greatscottgadgets/ubertooth/host/kismet/plugin-ubertooth-phyneutral/README

Kismet-Ubertooth-Phyneutral

-1. PHY NEUTRAL

    Kismet is currently (Spring/Summer 2011) undergoing a rewrite of the
    internal system for tracking networks to make Kismet truly phy-neutral,
    agnostic of the type of data being sniffed and type of devices being
    tracked.

    This branch of the Ubertooth Kismet plugin uses the phy-neutral
    extensions in Kismet.  It REQUIRES the LATEST svn of Kismet as
    phy-neutral is a rapidly moving target and is being co-developed with
    the Ubertooth plugin and the phy-neutral 802.11 components.  IT WILL NOT
    work with NON-BLEEDING-EDGE Kismet.  Every time you update the Ubertooth
    plugin code, update Kismet and recompile it at the same time!

0.  NOT COMPLETE

1.  What is Kismet-Ubertooth
2.  Caveats
3.  Compiling
4.  Installing
5.  Using

0.  NOT COMPLETE

*** THIS CODE IS CURRENTLY NOT COMPLETE ***

What it does:

* Control one (and only one) Ubertooth Zero or Ubertooth One
* Monitor one Bluetooth channel
* Display the LAP of Bluetooth packets
* Determine and display the UAP of Bluetooth packets
* Log to pcap file

What it should be able to do in the future:

* Determine the clock of a target piconets
* Hop along with a target piconet through all channels
* Control more than one Ubertooth Zero or Ubertooth One
* Read pcap files
* Print debug info about packets

1.  What is Kismet-Ubertooth

	Kismet-Ubertooth is a Kismet plugin which provides Bluetooth support in
	Kismet.  It relies on the Bluetooth baseband library, libbtbb 
	(https://github.com/greatscottgadgets/libbtbb). Kismet-Ubertooth
	performs passive monitoring of Bluetooth networks using the Ubertooth
	platform (https://github.com/greatscottgadgets/ubertooth).

	It CAN NOT BE USED with 802.11 wi-fi cards, it is a completely different
	protocol.  If you do not have an Ubertooth but have a Bluetooth adapter,
	try the btscan plugin instead.  It performs active scanning of discoverable
	Bluetooth devices.  Better yet, build yourself an Ubertooth One.

	Kismet-Ubertooth defines the decoders, loggers, and UI controls for
	Bluetooth networks in a common fashion, and supports reading and writing
	Bluetooth baseband pcap files.

	The Bluetooth baseband protocol is the air interface of Bluetooth.  It
	operates in the 2.4 GHz ISM band.  There is a separate interface known as
	HCI (Host Controller Interface) that operates between a host computer and
	an attached Bluetooth adapter.  Kismet-Ubertooth uses special hardware to
	directly access the baseband layer.  It does not operate at the HCI layer.
	Try hcidump if you want to access HCI.

2.  Caveats

	This code is currently only partially developed and may not provide full
	functionality.

	This code has only been tested on Linux.  This code MAY work on other
	platforms, but currently it is only developed with Linux as a target.

3.  Compiling

	Compiling the Kismet-Ubertooth plugin requires the Kismet source be
	installed and configured.  The libbtbb library (0.5 or higher) and libusb
	(1.0 or higher) must also be installed.

	By default, Kismet-Ubertooth expects the Kismet source to be in
	/usr/src/kismet; this can be overridden by setting the KIS_SRC_DIR
	environment variable:

		cd plugin-ubertooth
		KIS_SRC_DIR=/home/foo/src/kismet make

4.  Installing

	Kismet plugins may be installed system-wide in the plugins directory (by
	default, /usr/local/lib/kismet/) or in the users home directory
	(~/.kismet/plugins).

	To install in the system-wide directory:

        cd plugin-ubertooth
        KIS_SRC_DIR=/home/foo/src/kismet make install

    Plugins can be installed in the current users home directory with:

        cd plugin-ubertooth
        make userinstall

5.  Using

	Once the plugin is loaded, Kismet will automatically understand and
	decode pcap files with the Bluetooth link data.

	To capture from an Ubertooth Zero or Ubertooth One, plug in the USB device,
	and define a capture source in Kismet using the interface 'ubertooth'.  The
	device will be automatically detected.

	If you have multiple Ubertooth devices connected, Kismet-Ubertooth uses the
	first one it finds.  Kismet-Ubertooth currently is not capable of using
	multiple Ubertooth devices simultaneously.

	To enable pcap logging, the logfile must be turned on by adding
	'pcapbtbb' to the logtypes= line of the kismet.conf.
