greatscottgadgets/ubertooth/hardware/endive/endive.sch

## KiCad design hardware/endive/endive.sch (2011-09-12)

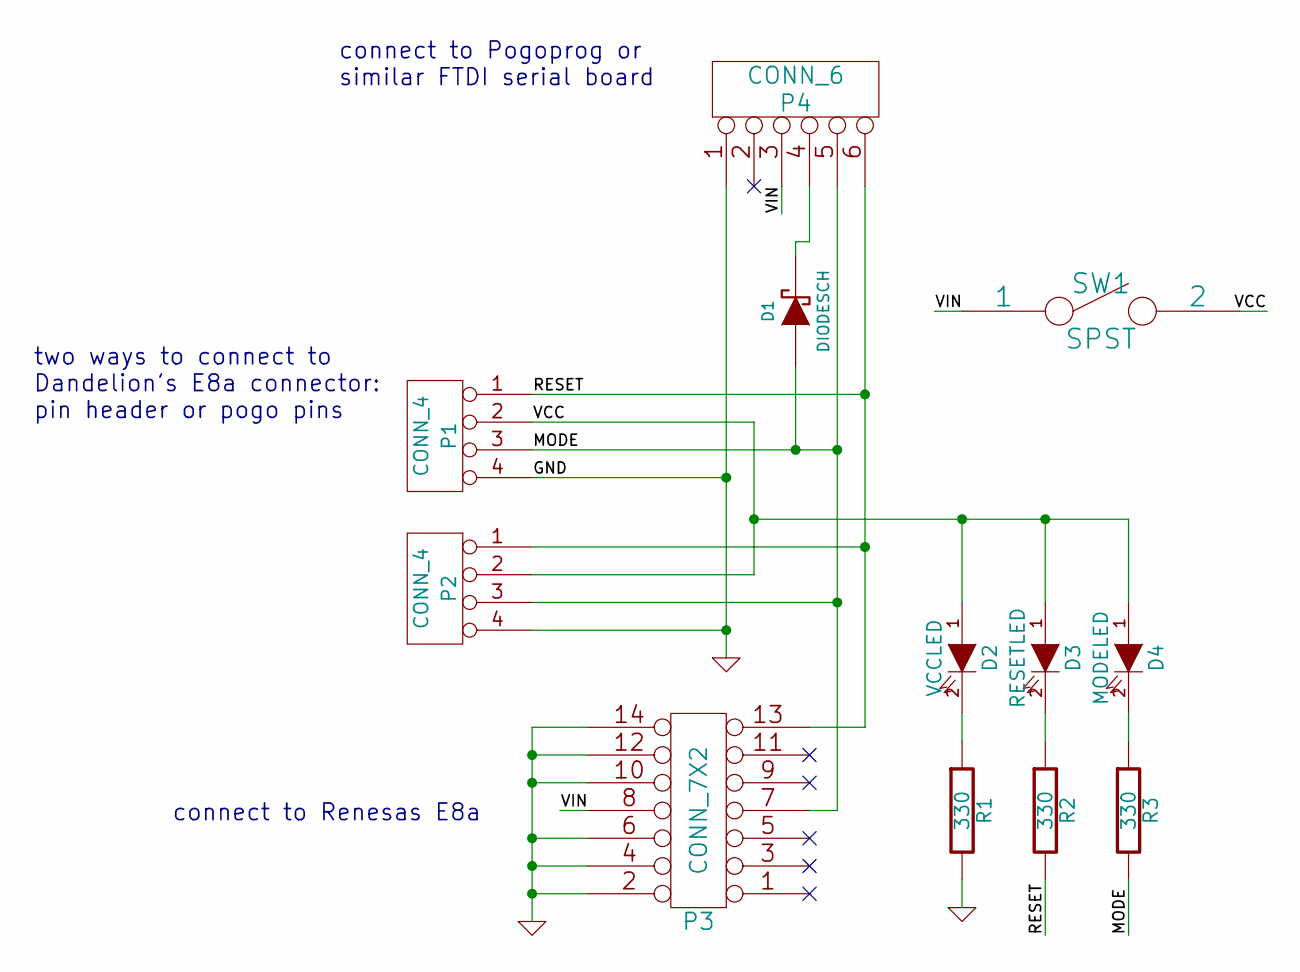
[picture p11: schematic endive.sch]

Parts:
D1: DIODESCH
D2: VCCLED
D3: RESETLED
D4: MODELED
P1, P2: CONN_4
P3: CONN_7X2
P4: CONN_6
R1, R2, R3: 330
SW1: SPST

Connections:
GND: P1.4, P2.4, P3.2, P3.4, P3.6, P3.10, P3.12, P3.14, P4.1, R1.2
MODE: D1.1 (A), P1.3, P2.3, P3.7, P4.5, R3.2
unnamed: D1.2 (K), P4.4
unnamed: D2.2 (K), R1.1
unnamed: D3.2 (K), R2.1
unnamed: D4.2 (K), R3.1
RESET: P1.1, P2.1, P3.13, P4.6, R2.2
VCC: D2.1 (A), D3.1 (A), D4.1 (A), P1.2, P2.2, SW1.2
VIN: P3.8, P4.3, SW1.1

Notes on the sheet:
connect to Renesas E8a
connect to Pogoprog or similar FTDI serial board
two ways to connect to Dandelion's E8a connector: pin header or pogo pins
