greatscottgadgets/ubertooth/hardware/pogoprog/pogoprog.sch

## KiCad design hardware/pogoprog/pogoprog.sch (2021-12-16)

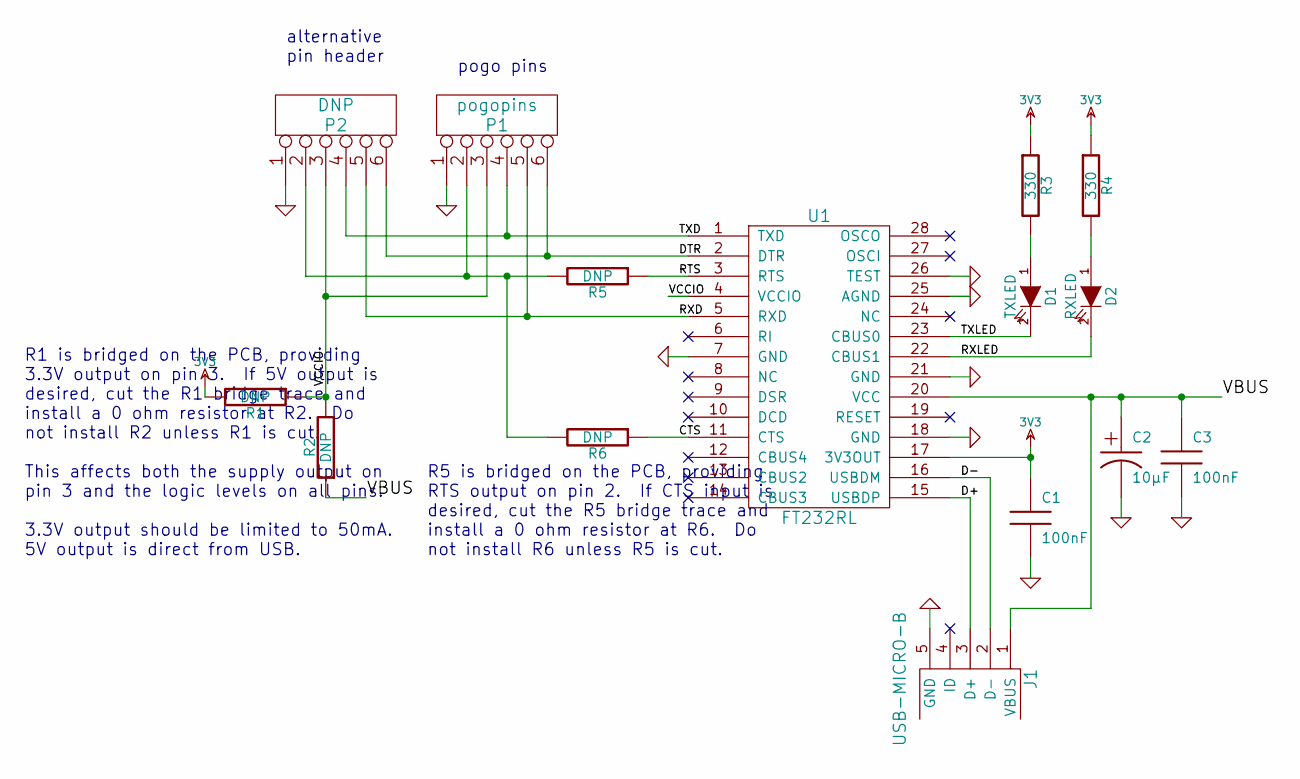
[picture p12: schematic pogoprog.sch]

Parts:
C1, C3: 100nF
C2: 10μF
D1: TXLED
D2: RXLED
J1: USB-MICRO-B
P1: pogopins
P2: DNP
R1, R2, R5, R6: DNP
R3, R4: 330
U1: FT232RL

Connections:
3V3: C1.1, R1.2, R3.1, R4.1, U1.17 (3V3OUT)
CTS: R6.1, U1.11 (CTS)
D+: J1.3 (D+), U1.15 (USBDP)
D-: J1.2 (D-), U1.16 (USBDM)
DTR: P1.6, P2.6, U1.2 (DTR)
GND: C1.2, C2.2, C3.2, J1.5 (GND), P1.1, P2.1, U1.7 (GND), U1.18 (GND), U1.21 (GND), U1.25 (AGND), U1.26 (TEST)
unnamed: D1.1 (A), R3.2
unnamed: D2.1 (A), R4.2
unnamed: P1.2, P2.2, R5.2, R6.2
RTS: R5.1, U1.3 (RTS)
RXD: P1.5, P2.5, U1.5 (RXD)
RXLED: D2.2 (K), U1.22 (CBUS1)
TXD: P1.4, P2.4, U1.1 (TXD)
TXLED: D1.2 (K), U1.23 (CBUS0)
VBUS: C2.1, C3.1, J1.1 (VBUS), R2.1, U1.20 (VCC)
VCCIO: P1.3, P2.3, R1.1, R2.2, U1.4 (VCCIO)

Notes on the sheet:
R5 is bridged on the PCB, providing RTS output on pin 2. If CTS input is desired, cut the R5 bridge trace and install a 0 ohm resistor at R6. Do not install R6 unless R5 is cut.
R1 is bridged on the PCB, providing 3.3V output on pin 3. If 5V output is desired, cut the R1 bridge trace and install a 0 ohm resistor at R2. Do not install R2 unless R1 is cut. This affects both the supply output on pin 3 and the logic levels on all pins. 3.3V output should be limited to 50mA. 5V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
alternative pin header
pogo pins
