greatscottgadgets/ubertooth/hardware/ubertooth-one/ubertooth-one.sch

## KiCad design hardware/ubertooth-one/ubertooth-one.sch (2021-12-16)

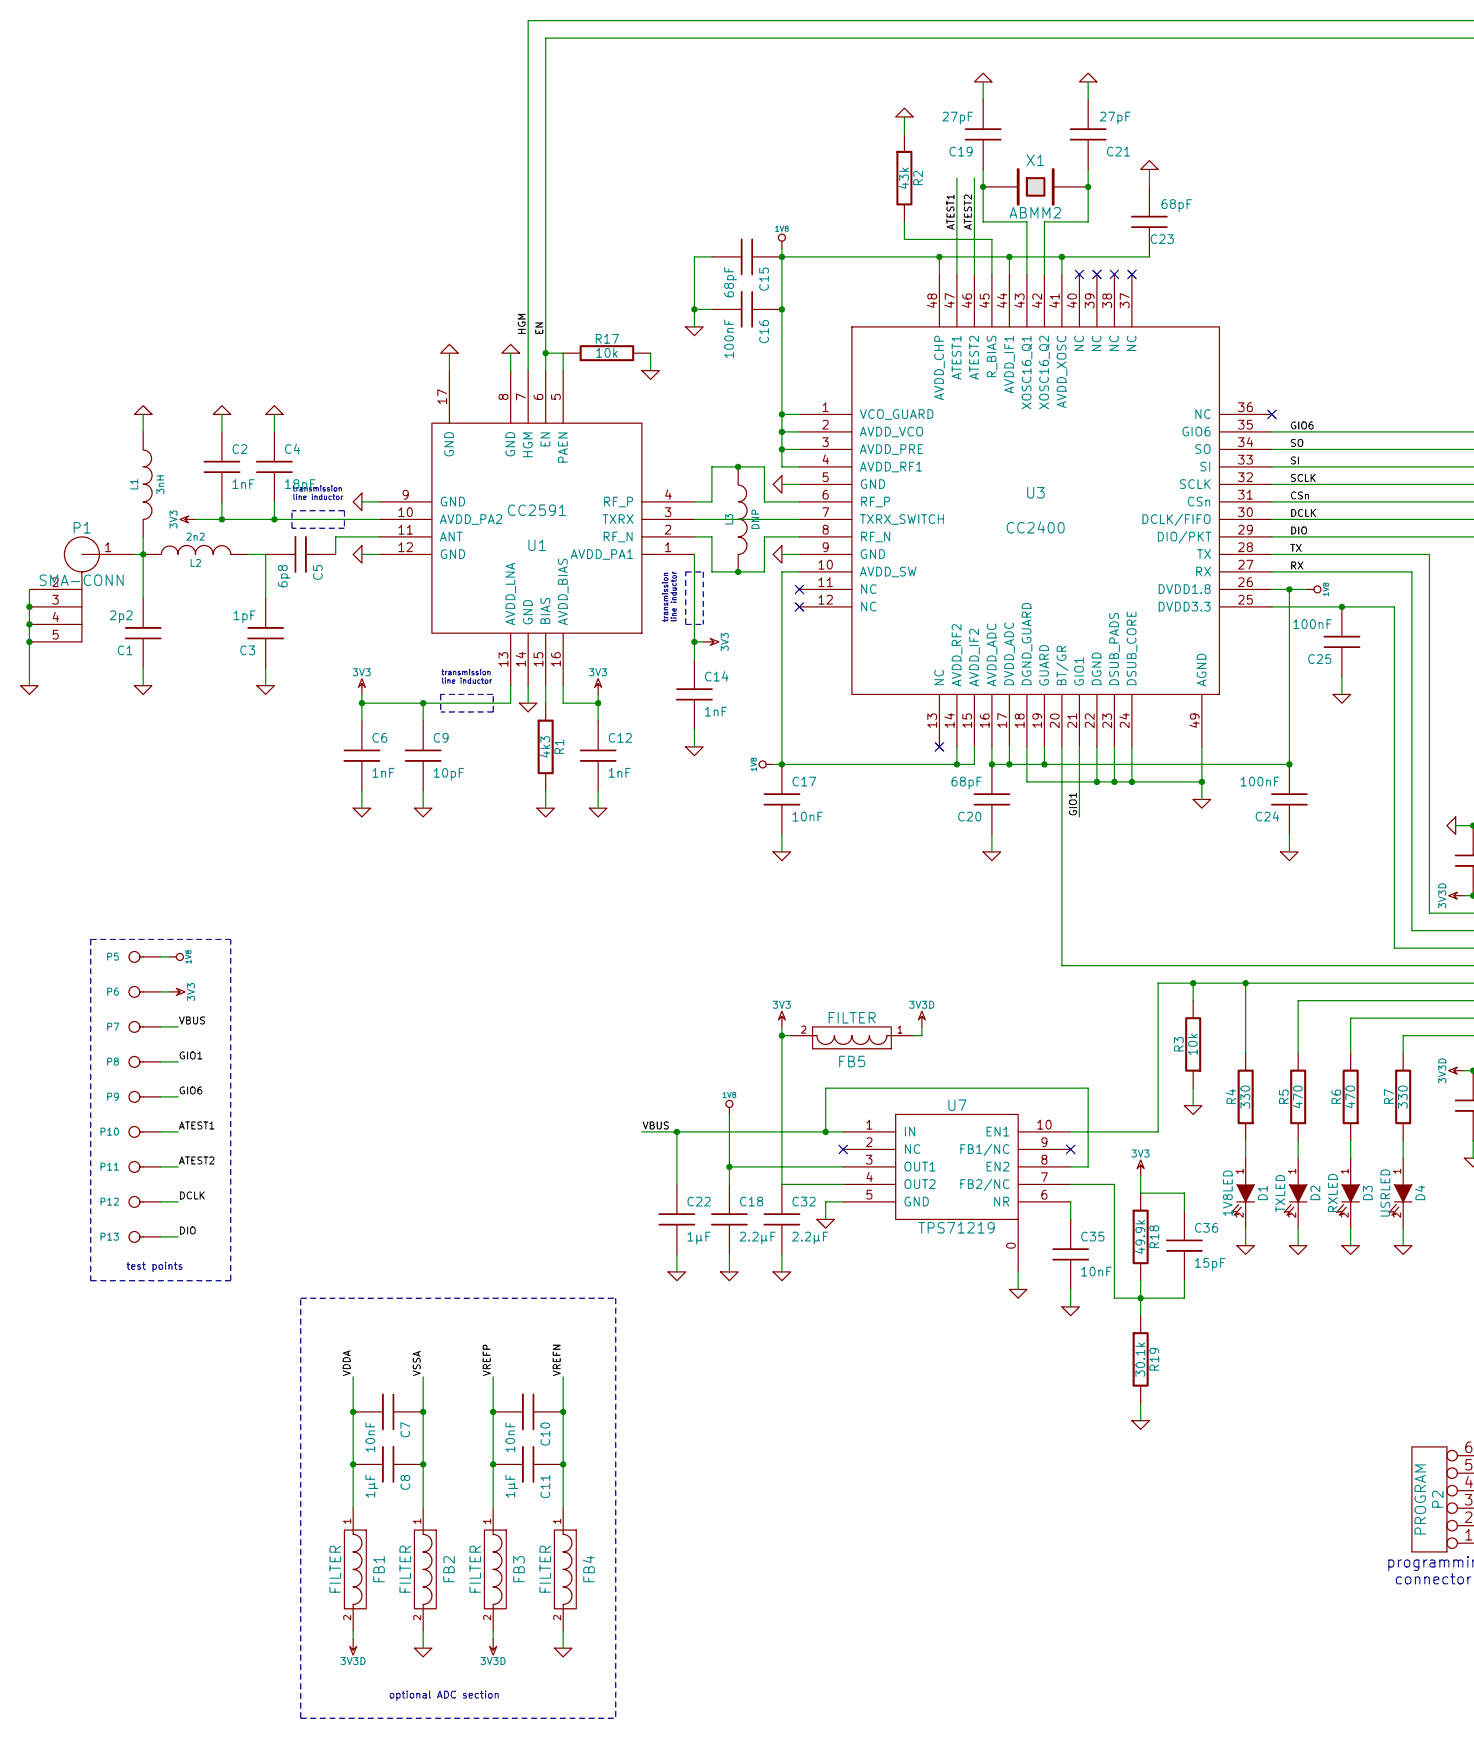
[picture p15: schematic ubertooth-one.sch, part in row 1, column 1]

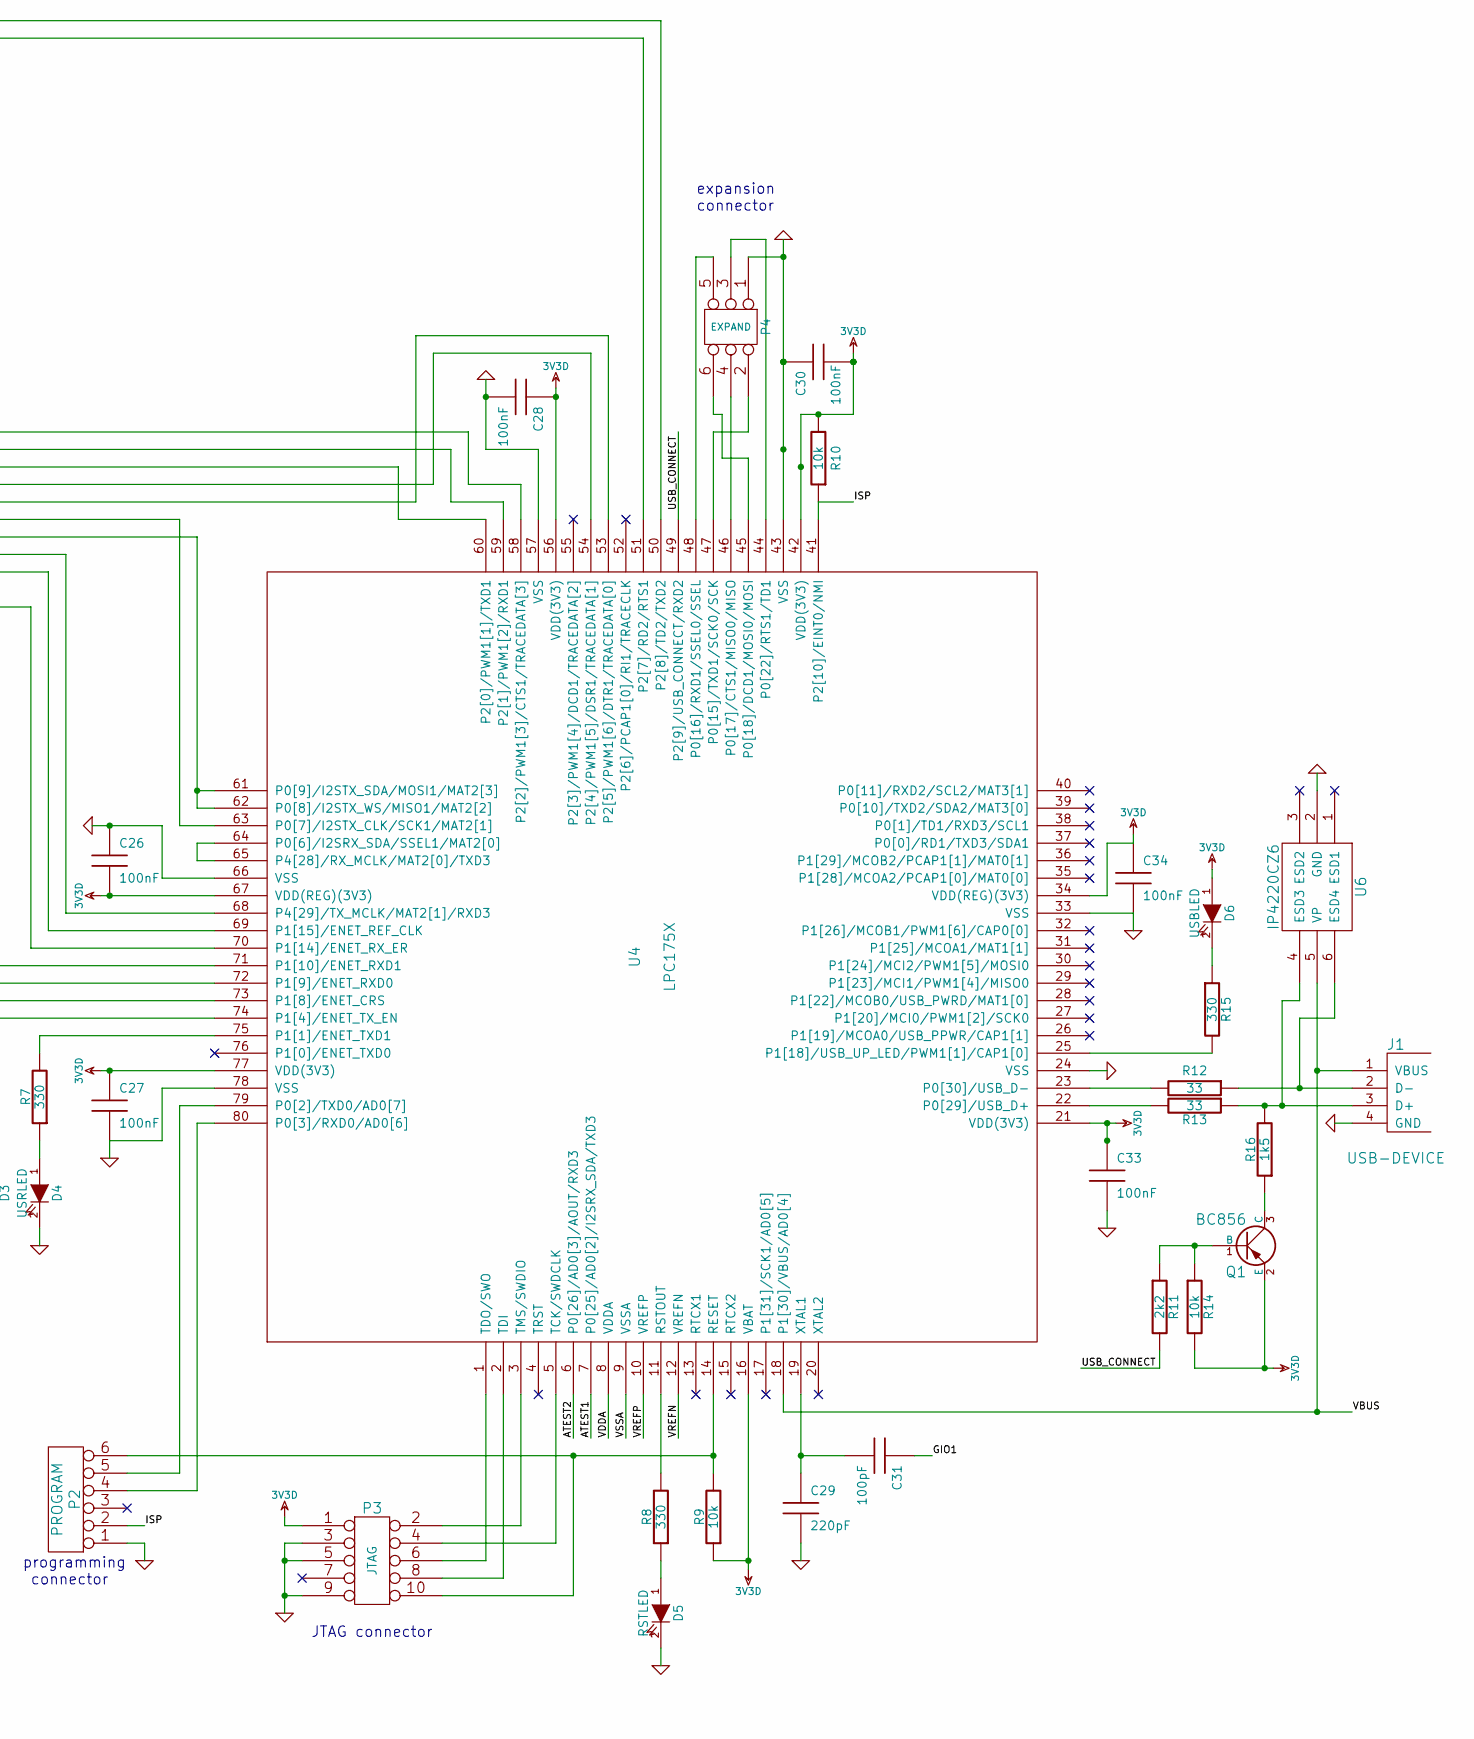
[picture p16: schematic ubertooth-one.sch, part in row 1, column 2]

Parts:
C1: 2p2; 0402
C2, C6, C12, C14: 1nF; 0402
C3: 1pF; 0402
C4: 18pF; 0402
C5: 6p8; 0402
C7, C10, C35: 10nF; 0603
C8, C11, C22: 1µF; 0603
C9: 10pF; 0402
C15, C20, C23: 68pF; 0402
C16, C24, C25: 100nF; 0402
C17: 10nF; 0402
C18, C32: 2.2µF; 0603
C19, C21: 27pF; 0603
C26, C27, C28, C30, C33, C34: 100nF; 0603
C29: 220pF; 0603
C31: 100pF; 0603
C36: 15pF; 0603
D1: 1V8LED; 0603D
D2: TXLED; 0603D
D3: RXLED; 0603D
D4: USRLED; 0603D
D5: RSTLED; 0603D
D6: USBLED; 0603D
FB1, FB2, FB3, FB4: FILTER; 0603bridged
FB5: FILTER; 0603
J1: USB-DEVICE; USB-A-USAM-04
L1: 3nH; 0402
L2: 2n2; 0402
L3: DNP; 0402gap
P1: SMA-CONN; SMA-EDGE
P2: PROGRAM; 100MIL-HEADER-1X6-EDGE
P3: JTAG; 50MIL-HEADER-2X5-TH
P4: EXPAND; PIN_ARRAY_3X2
P5: 1V8; testpad-50mil
P6: 3V3; testpad-50mil
P7: VBUS; testpad-50mil
P8: GIO1; testpad-50mil
P9: GIO6; testpad-50mil
P10: ATEST1; testpad-50mil
P11: ATEST2; testpad-50mil
P12: DCLK; testpad-50mil
P13: DIO; testpad-50mil
Q1: BC856; SOT416
R1: 4k3; 0402
R2: 43k; 0402
R3, R9, R10, R14, R17: 10k; 0603
R4, R7, R8, R15: 330; 0603
R5, R6: 470; 0603
R11: 2k2; 0603
R12, R13: 33; 0603
R16: 1k5; 0603
R18: 49.9k; 0603
R19: 30.1k; 0603
U1: CC2591; VQFN16
U3: CC2400; QFN48
U4: LPC175X; LQFP80
U6: IP4220CZ6; SOT457
U7: TPS71219; S-PVSON-N10
X1: ABMM2

Connections:
1V8: C15.1, C16.1, C17.1, C18.1, C20.2, C23.1, C24.2, P5.1, U3.1 (VCO_GUARD), U3.2 (AVDD_VCO), U3.3 (AVDD_PRE), U3.4 (AVDD_RF1), U3.10 (AVDD_SW), U3.14 (AVDD_RF2), U3.15 (AVDD_IF2), U3.16 (AVDD_ADC), U3.17 (DVDD_ADC), U3.19 (GUARD), U3.26 (DVDD1.8), U3.41 (AVDD_XOSC), U3.44 (AVDD_IF1), U3.48 (AVDD_CHP), U7.3 (OUT1)
3V3: C2.2, C4.2, C6.1, C9.1, C12.1, C14.1, C32.1, C36.1, FB5.2, P6.1, R18.1, U1.1 (AVDD_PA1), U1.10 (AVDD_PA2), U1.13 (AVDD_LNA), U1.16 (AVDD_BIAS), U7.4 (OUT2)
3V3D: C26.2, C27.1, C28.1, C30.2, C33.1, C34.1, D6.1 (A), FB1.2, FB3.2, FB5.1, P3.1, Q1.2 (E), R9.1, R10.2, R14.2, U4.16 (VBAT), U4.21 (VDD(3V3)), U4.34 (VDD(REG)(3V3)), U4.42 (VDD(3V3)), U4.56 (VDD(3V3)), U4.67 (VDD(REG)(3V3)), U4.77 (VDD(3V3))
ATEST1: P10.1, U3.47 (ATEST1), U4.7 (P0[25]/AD0[2]/I2SRX_SDA/TXD3)
ATEST2: P11.1, U3.46 (ATEST2), U4.6 (P0[26]/AD0[3]/AOUT/RXD3)
CSn: U3.31 (CSn), U4.53 (P2[5]/PWM1[6]/DTR1/TRACEDATA[0])
DCLK: P12.1, U3.30 (DCLK/FIFO), U4.63 (P0[7]/I2STX_CLK/SCK1/MAT2[1])
DIO: P13.1, U3.29 (DIO/PKT), U4.61 (P0[9]/I2STX_SDA/MOSI1/MAT2[3]), U4.62 (P0[8]/I2STX_WS/MISO1/MAT2[2])
EN: R17.1, U1.5 (PAEN), U1.6 (EN), U4.51 (P2[7]/RD2/RTS1)
GIO1: C31.1, P8.1, U3.21 (GIO1)
GIO6: P9.1, U3.35 (GIO6), U4.58 (P2[2]/PWM1[3]/CTS1/TRACEDATA[3])
GND: C1.1, C2.1, C3.1, C4.1, C6.2, C9.2, C12.2, C14.2, C15.2, C16.2, C17.2, C18.2, C19.2, C20.1, C21.2, C22.2, C23.2, C24.1, C25.1, C26.1, C27.2, C28.2, C29.2, C30.1, C32.2, C33.2, C34.2, C35.2, D1.2 (K), D2.2 (K), D3.2 (K), D4.2 (K), D5.2 (K), FB2.2, FB4.2, J1.4 (GND), L1.1, P1.2 (GND), P1.3 (GND), P1.4 (GND), P1.5 (GND), P2.1, P3.3, P3.5, P3.9, P4.1, R1.2, R2.1, R3.1, R17.2, R19.2, U1.8 (GND), U1.9 (GND), U1.12 (GND), U1.14 (GND), U1.17 (GND), U3.5 (GND), U3.9 (GND), U3.18 (DGND_GUARD), U3.22 (DGND), U3.23 (DSUB_PADS), U3.24 (DSUB_CORE), U3.49 (AGND), U4.24 (VSS), U4.33 (VSS), U4.43 (VSS), U4.57 (VSS), U4.66 (VSS), U4.78 (VSS), U6.2 (GND), U7.0, U7.5 (GND)
HGM: U1.7 (HGM), U4.50 (P2[8]/TD2/TXD2)
ISP: P2.2, R10.1, U4.41 (P2[10]/EINT0/NMI)
unnamed: C1.2, L1.2, L2.1, P1.1 (RF)
unnamed: C3.2, C5.2, L2.2
unnamed: C5.1, U1.11 (ANT)
unnamed: C19.1, U3.43 (XOSC16_Q1), X1.1
unnamed: C21.1, U3.42 (XOSC16_Q2), X1.2
unnamed: C25.2, U3.25 (DVDD3.3), U4.70 (P1[14]/ENET_RX_ER)
unnamed: C29.1, C31.2, U4.19 (XTAL1)
unnamed: C35.1, U7.6 (NR)
unnamed: C36.2, R18.2, R19.1, U7.7 (FB2/NC)
unnamed: D1.1 (A), R4.1
unnamed: D2.1 (A), R5.1
unnamed: D3.1 (A), R6.1
unnamed: D4.1 (A), R7.1
unnamed: D5.1 (A), R8.1
unnamed: D6.2 (K), R15.1
unnamed: J1.2 (D-), R12.1, U6.6 (ESD4)
unnamed: J1.3 (D+), R13.1, R16.2, U6.4 (ESD3)
unnamed: L3.1, U1.4 (RF_P), U3.6 (RF_P)
unnamed: L3.2, U1.2 (RF_N), U3.8 (RF_N)
unnamed: P2.4, U4.80 (P0[3]/RXD0/AD0[6])
unnamed: P2.5, U4.79 (P0[2]/TXD0/AD0[7])
unnamed: P2.6, P3.10, R9.2, U4.14 (RESET)
unnamed: P3.2, U4.3 (TMS/SWDIO)
unnamed: P3.4, U4.5 (TCK/SWDCLK)
unnamed: P3.6, U4.1 (TDO/SWO)
unnamed: P3.8, U4.2 (TDI)
unnamed: P4.2, U4.47 (P0[15]/TXD1/SCK0/SCK)
unnamed: P4.3, U4.44 (P0[22]/RTS1/TD1)
unnamed: P4.4, U4.46 (P0[17]/CTS1/MISO0/MISO)
unnamed: P4.5, U4.48 (P0[16]/RXD1/SSEL0/SSEL)
unnamed: P4.6, U4.45 (P0[18]/DCD1/MOSI0/MOSI)
unnamed: Q1.1 (B), R11.1, R14.1
unnamed: Q1.3 (C), R16.1
unnamed: R1.1, U1.15 (BIAS)
unnamed: R2.2, U3.45 (R_BIAS)
unnamed: R3.2, R4.2, U4.72 (P1[9]/ENET_RXD0), U7.10 (EN1)
unnamed: R5.2, U4.73 (P1[8]/ENET_CRS)
unnamed: R6.2, U4.74 (P1[4]/ENET_TX_EN)
unnamed: R7.2, U4.75 (P1[1]/ENET_TXD1)
unnamed: R8.2, U4.11 (RSTOUT)
unnamed: R12.2, U4.23 (P0[30]/USB_D-)
unnamed: R13.2, U4.22 (P0[29]/USB_D+)
unnamed: R15.2, U4.25 (P1[18]/USB_UP_LED/PWM1[1]/CAP1[0])
unnamed: U1.3 (TXRX), U3.7 (TXRX_SWITCH)
unnamed: U3.20 (BT/GR), U4.71 (P1[10]/ENET_RXD1)
unnamed: U4.64 (P0[6]/I2SRX_SDA/SSEL1/MAT2[0]), U4.65 (P4[28]/RX_MCLK/MAT2[0]/TXD3)
RX: U3.27 (RX), U4.69 (P1[15]/ENET_REF_CLK)
SCLK: U3.32 (SCLK), U4.54 (P2[4]/PWM1[5]/DSR1/TRACEDATA[1])
SI: U3.33 (SI), U4.60 (P2[0]/PWM1[1]/TXD1)
SO: U3.34 (SO), U4.59 (P2[1]/PWM1[2]/RXD1)
TX: U3.28 (TX), U4.68 (P4[29]/TX_MCLK/MAT2[1]/RXD3)
USB_CONNECT: R11.2, U4.49 (P2[9]/USB_CONNECT/RXD2)
VBUS: C22.1, J1.1 (VBUS), P7.1, U4.18 (P1[30]/VBUS/AD0[4]), U6.5 (VP), U7.1 (IN), U7.8 (EN2)
VDDA: C7.2, C8.2, FB1.1, U4.8 (VDDA)
VREFN: C10.1, C11.1, FB4.1, U4.12 (VREFN)
VREFP: C10.2, C11.2, FB3.1, U4.10 (VREFP)
VSSA: C7.1, C8.1, FB2.1, U4.9 (VSSA)

Notes on the sheet:
test points
expansion connector
JTAG connector
programming connector
optional ADC section
transmission line inductor
