greatscottgadgets/ubertooth/firmware/common/ubertooth.h

/*
 * Copyright 2010, 2011 Michael Ossmann
 *
 * This file is part of Project Ubertooth.
 *
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
 * You should have received a copy of the GNU General Public License
 * along with this program; see the file COPYING.  If not, write to
 * the Free Software Foundation, Inc., 51 Franklin Street,
 * Boston, MA 02110-1301, USA.
 */

#ifndef __UBERTOOTH_H
#define __UBERTOOTH_H

#include "lpc17.h"
#include "types.h"
#include "cc2400.h"
#include "ubertooth_interface.h"

typedef void (*IAP_ENTRY)(u32[], u32[]);
extern const IAP_ENTRY iap_entry;

/* operating modes */
enum operating_modes {
	MODE_IDLE          = 0,
	MODE_RX_SYMBOLS    = 1,
	MODE_TX_SYMBOLS    = 2,
	MODE_TX_TEST       = 3,
	MODE_SPECAN        = 4,
	MODE_RANGE_TEST    = 5,
	MODE_REPEATER      = 6,
	MODE_LED_SPECAN    = 7,
	MODE_BT_FOLLOW     = 8,
	MODE_BT_FOLLOW_LE  = 9,
	MODE_BT_PROMISC_LE = 10,
	MODE_RESET         = 11,
	MODE_BT_SLAVE_LE   = 12,
	MODE_EGO           = 13,
	MODE_AFH           = 14,
	MODE_RX_GENERIC    = 15,
	MODE_TX_GENERIC    = 16,
	MODE_XMAS          = 17,
};

/* hardware identification number */
#define BOARD_ID_UBERTOOTH_ZERO 0
#define BOARD_ID_UBERTOOTH_ONE  1
#define BOARD_ID_TC13BADGE      2

#ifdef UBERTOOTH_ZERO
#define BOARD_ID BOARD_ID_UBERTOOTH_ZERO
#endif
#ifdef UBERTOOTH_ONE
#define BOARD_ID BOARD_ID_UBERTOOTH_ONE
#endif
#ifdef TC13BADGE
#define BOARD_ID BOARD_ID_TC13BADGE
#endif

/* GPIO pins */
#ifdef UBERTOOTH_ZERO
#define PIN_USRLED (1 << 11) /* P0.11 */
#define PIN_RXLED  (1 << 28) /* P4.28 */
#define PIN_TXLED  (1 << 29) /* P4.29 */
#define PIN_CC1V8  (1 << 29) /* P1.29 */
#define PIN_CC3V3  (1 << 0 ) /* P1.0  */
#define PIN_VBUS   (1 << 30) /* P1.30 */
#define PIN_RX     (1 << 1 ) /* P1.1  */
#define PIN_TX     (1 << 4 ) /* P1.4  */
#define PIN_CSN    (1 << 8 ) /* P1.8  */
#define PIN_SCLK   (1 << 9 ) /* P1.9  */
#define PIN_MOSI   (1 << 10) /* P1.10 */
#define PIN_MISO   (1 << 14) /* P1.14 */
#define PIN_GIO6   (1 << 15) /* P1.15 */
#define PIN_BTGR   (1 << 31) /* P1.31 */
#define PIN_SSEL0  (1 << 9 ) /* P2.9  */
#endif
#ifdef UBERTOOTH_ONE
#define PIN_USRLED (1 << 1 ) /* P1.1  */
#define PIN_RXLED  (1 << 4 ) /* P1.4  */
#define PIN_TXLED  (1 << 8 ) /* P1.8  */
#define PIN_CC1V8  (1 << 9 ) /* P1.9  */
#define PIN_CC3V3  (1 << 14) /* P1.14 */
#define PIN_VBUS   (1 << 30) /* P1.30 */
#define PIN_RX     (1 << 15) /* P1.15 */
#define PIN_TX     (1 << 29) /* P4.29 */
#define PIN_CSN    (1 << 5 ) /* P2.5  */
#define PIN_SCLK   (1 << 4 ) /* P2.4  */
#define PIN_MOSI   (1 << 0 ) /* P2.0  */
#define PIN_MISO   (1 << 1 ) /* P2.1  */
#define PIN_GIO6   (1 << 2 ) /* P2.2  */
#define PIN_BTGR   (1 << 10) /* P1.10 */
#define PIN_SSEL1  (1 << 28) /* P4.28 */
#define PIN_PAEN   (1 << 7 ) /* P2.7 */
#define PIN_HGM    (1 << 8 ) /* P2.8 */
#endif
#ifdef TC13BADGE
#define PIN_CC1V8    (1 << 0 ) /* P1.0  */
#define PIN_CC3V3    (1 << 14) /* P1.14 */
#define PIN_VBUS     (1 << 30) /* P1.30 */
#define PIN_DIGITAL2 (1 << 0 ) /* P2.0  */
#define PIN_DIGITAL3 (1 << 1 ) /* P2.1  */
#define PIN_DIGITAL4 (1 << 2 ) /* P2.2  */
#define PIN_DIGITAL5 (1 << 3 ) /* P2.3  */
#define PIN_DIGITAL6 (1 << 4 ) /* P2.4  */
#define PIN_DIGITAL7 (1 << 5 ) /* P2.5  */
#define PIN_DIGITAL8 (1 << 6 ) /* P2.6  */
#define PIN_DIGITAL9 (1 << 7 ) /* P2.7  */
#define PIN_SW1      (1 << 8 ) /* P2.8  */
#define PIN_CSN      (1 << 1 ) /* P1.1  */
#define PIN_SCLK     (1 << 4 ) /* P1.4  */
#define PIN_MOSI     (1 << 8 ) /* P1.8  */
#define PIN_MISO     (1 << 9 ) /* P1.9  */
#define PIN_GIO6     (1 << 10) /* P1.10 */
#define PIN_SSEL1    (1 << 28) /* P4.28 */
#define PIN_R8C_CTL  (1 << 22) /* P1.22 connects to R8C's P4_5 */
#define PIN_R8C_ACK  (1 << 19) /* P1.19 connects to R8C's P0_0 */
/* RX, TX, and BT/GR are fixed to ground on TC13BADGE */
#endif

/* indicator LED control */
#ifdef UBERTOOTH_ZERO
#define USRLED     (FIO0PIN & PIN_USRLED)
#define USRLED_SET (FIO0SET = PIN_USRLED)
#define USRLED_CLR (FIO0CLR = PIN_USRLED)
#define RXLED      (FIO4PIN & PIN_RXLED)
#define RXLED_SET  (FIO4SET = PIN_RXLED)
#define RXLED_CLR  (FIO4CLR = PIN_RXLED)
#define TXLED      (FIO4PIN & PIN_TXLED)
#define TXLED_SET  (FIO4SET = PIN_TXLED)
#define TXLED_CLR  (FIO4CLR = PIN_TXLED)
#endif
#ifdef UBERTOOTH_ONE
#define USRLED     (FIO1PIN & PIN_USRLED)
#define USRLED_SET (FIO1SET = PIN_USRLED)
#define USRLED_CLR (FIO1CLR = PIN_USRLED)
#define RXLED      (FIO1PIN & PIN_RXLED)
#define RXLED_SET  (FIO1SET = PIN_RXLED)
#define RXLED_CLR  (FIO1CLR = PIN_RXLED)
#define TXLED      (FIO1PIN & PIN_TXLED)
#define TXLED_SET  (FIO1SET = PIN_TXLED)
#define TXLED_CLR  (FIO1CLR = PIN_TXLED)
#endif
#ifdef TC13BADGE
//FIXME The LEDs need to be controlled by talking to the R8C.
#define USRLED     0
#define USRLED_SET
#define USRLED_CLR
#define RXLED      0
#define RXLED_SET
#define RXLED_CLR
#define TXLED      0
#define TXLED_SET
#define TXLED_CLR
#endif

/* SW1 button press */
#ifdef TC13BADGE
#define SW1 (FIO2PIN & PIN_SW1)
#endif

/* R8C control */
#ifdef TC13BADGE
#define R8C_CTL_SET (FIO1SET = PIN_R8C_CTL)
#define R8C_CTL_CLR (FIO1CLR = PIN_R8C_CTL)
#define R8C_ACK     (FIO1PIN & PIN_R8C_ACK)
#endif

/* SSEL (SPI slave select) control for CC2400 DIO (un-buffered) serial */
#ifdef UBERTOOTH_ZERO
#define DIO_SSEL_SET  (FIO2SET = PIN_SSEL0)
#define DIO_SSEL_CLR  (FIO2CLR = PIN_SSEL0)
#endif
#if defined UBERTOOTH_ONE || defined TC13BADGE
#define DIO_SSEL_SET  (FIO4SET = PIN_SSEL1)
#define DIO_SSEL_CLR  (FIO4CLR = PIN_SSEL1)
#endif

/* 1V8 regulator control */
#define CC1V8      (FIO1PIN & PIN_CC1V8)
#define CC1V8_SET  (FIO1SET = PIN_CC1V8)
#define CC1V8_CLR  (FIO1CLR = PIN_CC1V8)

/* CC2400 control */
#ifdef UBERTOOTH_ZERO
#define CC3V3_SET  (FIO1SET = PIN_CC3V3)
#define CC3V3_CLR  (FIO1CLR = PIN_CC3V3)
#define RX_SET     (FIO1SET = PIN_RX)
#define RX_CLR     (FIO1CLR = PIN_RX)
#define TX_SET     (FIO1SET = PIN_TX)
#define TX_CLR     (FIO1CLR = PIN_TX)
#define CSN_SET    (FIO1SET = PIN_CSN)
#define CSN_CLR    (FIO1CLR = PIN_CSN)
#define SCLK_SET   (FIO1SET = PIN_SCLK)
#define SCLK_CLR   (FIO1CLR = PIN_SCLK)
#define MOSI_SET   (FIO1SET = PIN_MOSI)
#define MOSI_CLR   (FIO1CLR = PIN_MOSI)
#define GIO6       (FIO2PIN & PIN_GIO6)
#define GIO6_SET   (FIO1SET = PIN_GIO6)
#define GIO6_CLR   (FIO1CLR = PIN_GIO6)
#define BTGR_SET   (FIO1SET = PIN_BTGR)
#define BTGR_CLR   (FIO1CLR = PIN_BTGR)
#define MISO       (FIO1PIN & PIN_MISO)
#endif
#ifdef UBERTOOTH_ONE
#define CC3V3_SET  (FIO1SET = PIN_CC3V3)
#define CC3V3_CLR  (FIO1CLR = PIN_CC3V3)
#define RX_SET     (FIO1SET = PIN_RX)
#define RX_CLR     (FIO1CLR = PIN_RX)
#define TX_SET     (FIO4SET = PIN_TX)
#define TX_CLR     (FIO4CLR = PIN_TX)
#define CSN_SET    (FIO2SET = PIN_CSN)
#define CSN_CLR    (FIO2CLR = PIN_CSN)
#define SCLK_SET   (FIO2SET = PIN_SCLK)
#define SCLK_CLR   (FIO2CLR = PIN_SCLK)
#define MOSI_SET   (FIO2SET = PIN_MOSI)
#define MOSI_CLR   (FIO2CLR = PIN_MOSI)
#define GIO6       (FIO2PIN & PIN_GIO6)
#define GIO6_SET   (FIO2SET = PIN_GIO6)
#define GIO6_CLR   (FIO2CLR = PIN_GIO6)
#define BTGR_SET   (FIO1SET = PIN_BTGR)
#define BTGR_CLR   (FIO1CLR = PIN_BTGR)
#define MISO       (FIO2PIN & PIN_MISO)
#endif
#ifdef TC13BADGE
#define CC3V3_SET  (FIO1SET = PIN_CC3V3)
#define CC3V3_CLR  (FIO1CLR = PIN_CC3V3)
#define CSN_SET    (FIO1SET = PIN_CSN)
#define CSN_CLR    (FIO1CLR = PIN_CSN)
#define SCLK_SET   (FIO1SET = PIN_SCLK)
#define SCLK_CLR   (FIO1CLR = PIN_SCLK)
#define MOSI_SET   (FIO1SET = PIN_MOSI)
#define MOSI_CLR   (FIO1CLR = PIN_MOSI)
#define GIO6       (FIO2PIN & PIN_GIO6)
#define GIO6_SET   (FIO1SET = PIN_GIO6)
#define GIO6_CLR   (FIO1CLR = PIN_GIO6)
#define MISO       (FIO1PIN & PIN_MISO)
#endif

/*
 * DIO_SSP is the SSP assigned to the CC2400's secondary ("un-buffered") serial
 * interface
 */
#ifdef UBERTOOTH_ZERO
#define DIO_SSP_CR0   SSP0CR0
#define DIO_SSP_CR1   SSP0CR1
#define DIO_SSP_DR    SSP0DR
#define DIO_SSP_DMACR SSP0DMACR
#define DIO_SSP_SRC   (1 << 1) /* for DMACCxConfig register */
#endif
#if defined UBERTOOTH_ONE || defined TC13BADGE
#define DIO_SSP_CR0   SSP1CR0
#define DIO_SSP_CR1   SSP1CR1
#define DIO_SSP_DR    SSP1DR
#define DIO_SSP_DMACR SSP1DMACR
#define DIO_SSP_SRC   (3 << 1) /* for DMACCxConfig register */
#endif

/* CC2591 control */
#ifdef UBERTOOTH_ONE
#define PAEN     (FIO2PIN & PIN_PAEN)
#define PAEN_SET (FIO2SET = PIN_PAEN)
#define PAEN_CLR (FIO2CLR = PIN_PAEN)
#define HGM      (FIO2PIN & PIN_HGM)
#define HGM_SET  (FIO2SET = PIN_HGM)
#define HGM_CLR  (FIO2CLR = PIN_HGM)
#endif

/* USB VBUS monitoring */
#define VBUS (FIO1PIN & PIN_VBUS)

/*
 * clock configuration
 *
 * main oscillator:  16 MHz (from CC2400)
 * CPU clock (PLL0): 100 MHz
 * USB clock (PLL1): 48 MHz
 *
 * The ToorCon 13 badge is configured with a 30 MHz CPU clock instead of 100
 * MHz to reduce heat at the voltage regulator.  This is a sufficient clock
 * speed for passive Bluetooth monitoring.
 */
#ifdef TC13BADGE
#define MSEL0 14
#define NSEL0 0
#define CCLKSEL 15
#else
#define MSEL0 24
#define NSEL0 1
#define CCLKSEL 3
#endif
#define MSEL1 34
#define PSEL1 0

/* flash accelerator configuration */
#define FLASHTIM 0x4 /* up to 100 MHz CPU clock */

/*
 * bootloader_ctrl is a fixed memory location used for passing
 * information from the application to the bootloader across a reset
 */
extern uint32_t bootloader_ctrl;
#define DFU_MODE 0x4305BB21

void wait(u8 seconds);
void wait_ms(u32 ms);
void wait_us(u32 us);
u32 rbit(u32 value);
void gpio_init(void);
void all_pins_off(void);
void ubertooth_init(void);
void dio_ssp_init(void);
void atest_init(void);
void cc2400_init(void);
u32 cc2400_spi(u8 len, u32 data);
u16 cc2400_get(u8 reg);
void cc2400_set(u8 reg, u16 val);
u8 cc2400_get8(u8 reg);
void cc2400_set8(u8 reg, u8 val);
void cc2400_fifo_write(u8 len, u8 *data);
void cc2400_fifo_read(u8 len, u8 *buf);
u8 cc2400_status(void);
u8 cc2400_strobe(u8 reg);
void cc2400_reset(void);
void clock_start(void);
void reset(void);
void r8c_takeover(void);
void cc2400_tune_rx(uint16_t channel);
void cc2400_tune_tx(uint16_t channel);
void cc2400_hop_rx(uint16_t channel);
void cc2400_hop_tx(uint16_t channel);
void get_part_num(uint8_t *buffer, int *len);
void get_device_serial(uint8_t *buffer, int *len);
void set_isp(void);

#endif /* __UBERTOOTH_H */
