greatscottgadgets/ubertooth/firmware/bluetooth_rxtx/ubertooth_usb.c

/*
 * Copyright 2010 Michael Ossmann
 * Copyright 2013 Dominic Spill
 *
 * This file is part of Project Ubertooth.
 *
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
 * You should have received a copy of the GNU General Public License
 * along with this program; see the file COPYING.  If not, write to
 * the Free Software Foundation, Inc., 51 Franklin Street,
 * Boston, MA 02110-1301, USA.
 */

/*
	LPCUSB, an USB device driver for LPC microcontrollers
	Copyright (C) 2006 Bertrik Sikken (bertrik@sikken.nl)

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
	1. Redistributions of source code must retain the above copyright
	   notice, this list of conditions and the following disclaimer.
	2. Redistributions in binary form must reproduce the above copyright
	   notice, this list of conditions and the following disclaimer in the
	   documentation and/or other materials provided with the distribution.
	3. The name of the author may not be used to endorse or promote products
	   derived from this software without specific prior written permission.

	THIS SOFTWARE IS PROVIDED BY THE AUTHOR ``AS IS'' AND ANY EXPRESS OR
	IMPLIED WARRANTIES, INCLUDING, BUT NOT LIMITED TO, THE IMPLIED WARRANTIES
	OF MERCHANTABILITY AND FITNESS FOR A PARTICULAR PURPOSE ARE DISCLAIMED.
	IN NO EVENT SHALL THE AUTHOR BE LIABLE FOR ANY DIRECT, INDIRECT,
	INCIDENTAL, SPECIAL, EXEMPLARY, OR CONSEQUENTIAL DAMAGES (INCLUDING, BUT
	NOT LIMITED TO, PROCUREMENT OF SUBSTITUTE GOODS OR SERVICES; LOSS OF USE,
	DATA, OR PROFITS; OR BUSINESS INTERRUPTION) HOWEVER CAUSED AND ON ANY
	THEORY OF LIABILITY, WHETHER IN CONTRACT, STRICT LIABILITY, OR TORT
	(INCLUDING NEGLIGENCE OR OTHERWISE) ARISING IN ANY WAY OUT OF THE USE OF
	THIS SOFTWARE, EVEN IF ADVISED OF THE POSSIBILITY OF SUCH DAMAGE.
*/

#include "usbapi.h"
#include "usbhw_lpc.h"
#include "ubertooth.h"
#include "ubertooth_usb.h"
#include <string.h>

#ifdef UBERTOOTH_ZERO
#define ID_VENDOR 0x1D50
#define ID_PRODUCT 0x6000
#elif defined UBERTOOTH_ONE
#define ID_VENDOR 0x1D50
#define ID_PRODUCT 0x6002
#elif defined TC13BADGE
#define ID_VENDOR 0xFFFF
#define ID_PRODUCT 0x0004
#else
#define ID_VENDOR 0xFFFF
#define ID_PRODUCT 0x0004
#endif

#define BULK_IN_EP		0x82
#define BULK_OUT_EP		0x05

#define MAX_PACKET_SIZE	64

#define LE_WORD(x)		((x)&0xFF),((x)>>8)

/*
 * This is supposed to be a lock-free ring buffer, but I haven't verified
 * atomicity of the operations on head and tail.
 */

static u8 abDescriptors[] = {

/* Device descriptor */
	0x12,
	DESC_DEVICE,
	LE_WORD(0x0200),		// bcdUSB
	0xFF,              		// bDeviceClass
	0x00,              		// bDeviceSubClass
	0x00,              		// bDeviceProtocol
	MAX_PACKET_SIZE0,  		// bMaxPacketSize
	LE_WORD(ID_VENDOR),		// idVendor
	LE_WORD(ID_PRODUCT),		// idProduct
	LE_WORD(0x0107),		// bcdDevice
	0x01,              		// iManufacturer
	0x02,              		// iProduct
	0x03,              		// iSerialNumber
	0x01,              		// bNumConfigurations

// configuration
	0x09,
	DESC_CONFIGURATION,
	LE_WORD(0x20),  		// wTotalLength
	0x01,  					// bNumInterfaces
	0x01,  					// bConfigurationValue
	0x00,  					// iConfiguration
	0x80,  					// bmAttributes
	0x6e,  					// bMaxPower (220mA)

// interface
	0x09,
	DESC_INTERFACE,
	0x00,  		 			// bInterfaceNumber
	0x00,   				// bAlternateSetting
	0x02,   				// bNumEndPoints
	0xFF,   				// bInterfaceClass
	0x00,   				// bInterfaceSubClass
	0x00,   				// bInterfaceProtocol
	0x00,   				// iInterface

// bulk in
	0x07,
	DESC_ENDPOINT,
	BULK_IN_EP,				// bEndpointAddress
	0x02,   				// bmAttributes = BULK
	LE_WORD(MAX_PACKET_SIZE),// wMaxPacketSize
	0,						// bInterval

// bulk out
	0x07,
	DESC_ENDPOINT,
	BULK_OUT_EP,			// bEndpointAddress
	0x02,   				// bmAttributes = BULK
	LE_WORD(MAX_PACKET_SIZE),// wMaxPacketSize
	0,						// bInterval

// string descriptors
	0x04,
	DESC_STRING,
	LE_WORD(0x0409),

	// manufacturer string
	40,
	DESC_STRING,
	'G', 0x00,
	'r', 0x00,
	'e', 0x00,
	'a', 0x00,
	't', 0x00,
	' ', 0x00,
	'S', 0x00,
	'c', 0x00,
	'o', 0x00,
	't', 0x00,
	't', 0x00,
	' ', 0x00,
	'G', 0x00,
	'a', 0x00,
	'd', 0x00,
	'g', 0x00,
	'e', 0x00,
	't', 0x00,
	's', 0x00,

	// product string
	28,
	DESC_STRING,
	'U', 0x00,
	'b', 0x00,
	'e', 0x00,
	'r', 0x00,
	't', 0x00,
	'o', 0x00,
	'o', 0x00,
	't', 0x00,
	'h', 0x00,
	' ', 0x00,
	'O', 0x00,
	'n', 0x00,
	'e', 0x00,

	// serial number string
	0x42,
	DESC_STRING,
	'0', 0, '0', 0, '0', 0, '0', 0, '0', 0, '0', 0, '0', 0, '0', 0,
	'0', 0, '0', 0, '0', 0, '0', 0, '0', 0, '0', 0, '0', 0, '0', 0,
	'0', 0, '0', 0, '0', 0, '0', 0, '0', 0, '0', 0, '0', 0, '0', 0,
	'0', 0, '0', 0, '0', 0, '0', 0, '0', 0, '0', 0, '0', 0, '1', 0,

	// terminator
	0
};

#define USB_SERIAL_OFFSET 124

u8 abVendorReqData[258];

/* Unused functions
void usb_bulk_in_handler(u8 bEP, u8 bEPStatus)
{
	if (!(bEPStatus & EP_STATUS_DATA))
		dequeue_send();
}

void usb_bulk_out_handler(u8 bEP, u8 bEPStatus)
{
}
*/

VendorRequestHandler *v_req_handler;

BOOL usb_vendor_request_handler(TSetupPacket *pSetup, int *piLen, u8 **ppbData)
{
	int rv;
	u16 params[3] = {pSetup->wValue, pSetup->wIndex, pSetup->wLength};
	rv = v_req_handler(pSetup->bRequest, params, *ppbData, piLen);
	return (BOOL) (rv==1);
}


void set_serial_descriptor(u8 *descriptors) {
	u8 buf[17], *desc, nibble;
	int len, i;
	get_device_serial(buf, &len);
	if(buf[0] == 0) { /* IAP success */
		desc = descriptors + USB_SERIAL_OFFSET;
		for(i=0; i<16; i++) {
			nibble  = (buf[i+1]>>4) & 0xF;
			desc[i * 4] = (nibble > 9) ? ('a' + nibble - 10) : ('0' + nibble);
			desc[1+ i * 4] = 0;
			nibble = buf[i+1]&0xF;
			desc[2 + i * 4] = (nibble > 9) ? ('a' + nibble - 10) : ('0' + nibble);
			desc[3 + i * 4] = 0;
		}
	}
}

int ubertooth_usb_init(VendorRequestHandler *vendor_req_handler)
{
	// initialise stack
	USBInit();

	set_serial_descriptor(abDescriptors);
	
	// register device descriptors
	USBRegisterDescriptors(abDescriptors);

	// Request handler
	v_req_handler = vendor_req_handler;

	// override standard request handler
	USBRegisterRequestHandler(REQTYPE_TYPE_VENDOR, usb_vendor_request_handler, abVendorReqData);

	// register endpoints
	//USBHwRegisterEPIntHandler(BULK_IN_EP, usb_bulk_in_handler);
	//USBHwRegisterEPIntHandler(BULK_OUT_EP, usb_bulk_out_handler);

	// enable USB interrupts
	//ISER0 = ISER0_ISE_USB;

	// Enable WCID / driverless setup on Windows - Consumes Vendor Request 0xFF
	USBRegisterWinusbInterface(0xFF, "{8ac47a88-cc26-4aa9-887b-42ca8cf07a63}");

	// connect to bus
	USBHwConnect(TRUE);

	return 0;
}

usb_pkt_rx fifo[128];

volatile u32 head = 0;
volatile u32 tail = 0;

void usb_queue_init(void)
{
	head = 0;
	tail = 0;
	memset(fifo, 0, sizeof(fifo));
}

usb_pkt_rx *usb_enqueue(void)
{
	u8 h = head & 0x7F;
	u8 t = tail & 0x7F;
	u8 n = (t + 1) & 0x7F;

	/* fail if queue is full */
	if (h == n) {
		return NULL;
	}

	++tail;
	return &fifo[t];

}

usb_pkt_rx *dequeue(void)
{
	u8 h = head & 0x7F;
	u8 t = tail & 0x7F;

	/* fail if queue is empty */
	if (h == t) {
		return NULL;
	}

	++head;
	return &fifo[h];
}

#define USB_KEEP_ALIVE 400000
u32 last_usb_pkt = 0;  // for keep alive packets

int dequeue_send(u32 clkn)
{
	usb_pkt_rx *pkt = dequeue();
	if (pkt != NULL) {
		last_usb_pkt = clkn;
		USBHwEPWrite(BULK_IN_EP, (u8 *)pkt, sizeof(usb_pkt_rx));
		return 1;
	} else {
		if (clkn - last_usb_pkt > USB_KEEP_ALIVE) {
			u8 pkt_type = KEEP_ALIVE;
			last_usb_pkt = clkn;
			USBHwEPWrite(BULK_IN_EP, &pkt_type, 1);
		}
		return 0;
	}
}

void handle_usb(u32 clkn)
{
	u8 epstat;

	/* write queued packets to USB if possible */
	epstat = USBHwEPGetStatus(BULK_IN_EP);
	if (!(epstat & EPSTAT_B1FULL)) {
		dequeue_send(clkn);
	}
	if (!(epstat & EPSTAT_B2FULL)) {
		dequeue_send(clkn);
	}

	/* polled "interrupt" */
	USBHwISR();
}
