greatscottgadgets/ubertooth/firmware/bluetooth_rxtx/bluetooth_le.h

/*
 * Copyright 2012 Dominic Spill
 *
 * This file is part of Project Ubertooth.
 *
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
 * You should have received a copy of the GNU General Public License
 * along with this program; see the file COPYING.  If not, write to
 * the Free Software Foundation, Inc., 51 Franklin Street,
 * Boston, MA 02110-1301, USA.
 */

#include "ubertooth.h"

#define BTLE_CHANNELS 40
#define ADVERTISING_CHANNELS 3
#define DATA_CHANNELS 37

typedef enum {
    LINK_INACTIVE,
    LINK_LISTENING,
    LINK_CONN_PENDING,
    LINK_CONNECTED,
} link_state_t;

typedef struct _le_state_t {
    u32 access_address;         // Access Address to filter by
    u16 synch;                  // Access address in CC2400 syncword format
    u16 syncl;                  // lower 16 bits thereof
    u32 crc_init;               // CrcInit: used to calculate CRC
    u32 crc_init_reversed;      // bits-reversed version of the previous
    int crc_verify;             // true to reject packets with bad CRC

    link_state_t link_state;         // current link layer state

    u8 channel_idx;             // current channel index
    u8 channel_increment;       // amount to hop

    u32 conn_epoch;             // reference time for the start of the connection
    u16 volatile interval_timer;// number of intervals remaining before next hop
    u16 conn_interval;          // connection-specific hop interval
    u16 volatile conn_count;    // number of intervals since the start of the connection

    u8 win_size;                // window size (max packets per connection)
    u16 win_offset;             // offset of first window from start of connection

    int update_pending;         // whether a connection update is pending
    u16 update_instant;         // the connection count when the update takes effect
    u16 interval_update;        // the new hop_internal
    u8 win_size_update;         // the new window size
    u16 win_offset_update;      // the new window offset

    int do_follow;              // 1 if follow connections, 0 to only log advertising packets

    u8 target[6];               // target MAC for connection following (byte order reversed)
    u8 target_mask[6];          // mask for MAC connection following (byte order reversed)
    int target_set;             // whether a target has been set (default: false)
    u32 last_packet;            // when was the last packet received
} le_state_t;

// for handling LE channel maps
typedef struct _le_channel_remapping_t {
	int         channel_in_use[37];
	uint8_t     remapping_index[37]; // array of channel indices
	unsigned    total_channels;
} le_channel_remapping_t;

static const u8 whitening[] = {
    1, 1, 1, 1, 0, 1, 0, 1, 0, 1, 0, 0, 0, 0, 1, 0, 1, 1, 0, 1, 1, 1,
    1, 0, 0, 1, 1, 1, 0, 0, 1, 0, 1, 0, 1, 1, 0, 0, 1, 1, 0, 0, 0, 0,
    0, 1, 1, 0, 1, 1, 0, 1, 0, 1, 1, 1, 0, 1, 0, 0, 0, 1, 1, 0, 0, 1,
    0, 0, 0, 1, 0, 0, 0, 0, 0, 0, 1, 0, 0, 1, 0, 0, 1, 1, 0, 1, 0, 0,
    1, 1, 1, 1, 0, 1, 1, 1, 0, 0, 0, 0, 1, 1, 1, 1, 1, 1, 1, 0, 0, 0,
    1, 1, 1, 0, 1, 1, 0, 0, 0, 1, 0, 1, 0, 0, 1, 0, 1
};

static const u8 whitening_index[] = {
    70, 62, 120, 111, 77, 46, 15, 101, 66, 39, 31, 26, 80,
    83, 125, 89, 10, 35, 8, 54, 122, 17, 33, 0, 58, 115, 6,
    94, 86, 49, 52, 20, 40, 27, 84, 90, 63, 112, 47, 102
};

static const u8 hop_interval_lut[] = {
    0, 1, 19, 25, 28, 15, 31, 16, 14, 33, 26, 27, 34, 20, 8,
    5, 7, 24, 35, 2, 13, 30, 32, 29, 17, 3, 10, 11, 4, 23, 21,
    6, 22, 9, 12, 18, 36,
};

u16 btle_next_hop(le_state_t *le);
uint8_t btle_channel_index(uint16_t channel);
u16 btle_channel_index_to_phys(u8 idx);
u32 btle_calc_crc(u32 crc_init, u8 *data, int len);
u32 btle_reverse_crc(u32 crc, u8 *data, int len);
u32 btle_crcgen_lut(u32 crc_init, u8 *data, int len);
void le_dewhiten(uint8_t *data, unsigned size, unsigned channel);
void le_parse_channel_map(uint8_t *channel_map, le_channel_remapping_t *remapping);
uint8_t le_map_channel(uint8_t channel_idx, le_channel_remapping_t *remapping);

static const u32 whitening_word[40][12] = {
	{ 0xc3bcb240, 0x5f4a371f, 0x9a9cf685, 0x44c5d6c1, 0xe1de5920, 0xafa51b8f,
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
	  0xf8779648, 0xabe946e3, 0x33539ed0, 0x0898bad8, 0xfc3bcb24, 0x55f4a371, },
	{ 0xb240898b, 0x371fc3bc, 0xf6855f4a, 0xd6c19a9c, 0x592044c5, 0x1b8fe1de,
	  0x7b42afa5, 0xeb60cd4e, 0x2c902262, 0x8dc7f0ef, 0x3da157d2, 0x75b066a7, },
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
};
