greatscottgadgets/ubertooth/firmware/tc13badge/bitmaps.h

#define KEY_LEN 42
#define LOGO_LEN 546
#define ICON_LEN 65

const uint8_t key[KEY_LEN] = {
	0x20, 0xcc, 0x51, 0x51, 0x1f, 0xa4, 0x66,
	0x10, 0x01, 0x9c, 0x08, 0xe5, 0xd7, 0xfe,
	0x73, 0x04, 0x36, 0xbd, 0x59, 0x56, 0x2f,
	0xb5, 0xe9, 0x8a, 0xc1, 0x2b, 0x2b, 0x08,
	0xf1, 0xda, 0xe5, 0x61, 0x89, 0x7e, 0xcc,
	0xad, 0xbc, 0x91, 0x5b, 0x9c, 0xa5, 0x8a
	};

const uint8_t logo[LOGO_LEN][13] = {
	{0x20, 0xcc, 0x51, 0x51, 0x1f, 0xa4, 0x66, 0x10, 0x01, 0x36, 0xf7, 0xa1, 0xd7},
	{0xfe, 0x73, 0x04, 0x36, 0xb9, 0x59, 0x56, 0x2f, 0xb5, 0x43, 0x75, 0x88, 0x2b},
	{0x2b, 0x08, 0x79, 0xdb, 0xe5, 0x61, 0x9b, 0x7e, 0xcc, 0x07, 0x43, 0xbb, 0x5b},
	{0x9c, 0xe5, 0x8a, 0x2a, 0xec, 0x50, 0x13, 0x0f, 0xa6, 0xb3, 0xef, 0xac, 0x9c},
	{0x08, 0xe5, 0x5d, 0xef, 0x21, 0x00, 0x12, 0x34, 0x48, 0x38, 0xd0, 0x60, 0xe0},
	{0xca, 0xc8, 0x8e, 0x3e, 0x5d, 0x5b, 0x48, 0x88, 0x60, 0x76, 0x81, 0x67, 0x87},
	{0xfc, 0x9b, 0x36, 0xc6, 0xce, 0x24, 0x95, 0x62, 0x7b, 0xae, 0xe0, 0x1e, 0xd1},
	{0x10, 0x4a, 0x62, 0xd3, 0x3a, 0x6d, 0x09, 0xac, 0xdf, 0xc9, 0x42, 0xee, 0xa9},
	{0x2f, 0xc2, 0x36, 0x74, 0x7e, 0xd0, 0xd4, 0xd7, 0x8e, 0x25, 0x1a, 0x9e, 0x76},
	{0xfe, 0xa3, 0x52, 0x43, 0x6e, 0xa4, 0x63, 0x5a, 0x75, 0xdf, 0x33, 0xae, 0xae},
	{0x16, 0x5b, 0x99, 0xef, 0xfe, 0x63, 0xf7, 0x1a, 0x28, 0x01, 0x8c, 0xfb, 0xc9},
	{0x97, 0xa6, 0xa9, 0xd0, 0x4a, 0x16, 0x75, 0x3e, 0xd4, 0xd4, 0xf7, 0x0e, 0x25},
	{0x4f, 0x9e, 0x76, 0x81, 0x33, 0x52, 0x43, 0x6e, 0xa4, 0x63, 0x5a, 0x75, 0xdf},
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
	{0x61, 0x76, 0x7e, 0x67, 0x52, 0x40, 0x6e, 0x5b, 0x9c, 0xa5, 0x2a, 0x4f, 0xa1},
	{0x51, 0xac, 0x8c, 0xf0, 0x99, 0x10, 0xa9, 0x9c, 0x08, 0xe5, 0xd7, 0x01, 0xc5},
	{0x04, 0x9c, 0xe7, 0x1b, 0xfe, 0x2f, 0x9f, 0x69, 0x8a, 0xc1, 0x2b, 0xd4, 0xd3},
	{0x63, 0xfe, 0x30, 0x61, 0x89, 0x7e, 0x3b, 0xa9, 0xbc, 0x91, 0x5b, 0x63, 0xc8},
	{0xdd, 0xb0, 0x99, 0x51, 0x55, 0x1e, 0xc9, 0xf4, 0x10, 0x01, 0x9c, 0xf7, 0xb0},
	{0x81, 0xb4, 0x3b, 0x04, 0xc9, 0xb9, 0x71, 0x13, 0x2f, 0xb5, 0xe9, 0x75, 0x93},
	{0x9c, 0x63, 0x42, 0xf1, 0x24, 0x64, 0x61, 0xf6, 0x7e, 0xcc, 0xad, 0x43, 0xd1},
	{0xb4, 0x89, 0x05, 0x8b, 0xff, 0xec, 0x55, 0xaa, 0x1f, 0xa4, 0x66, 0xef, 0x01},
	{0x71, 0x5e, 0xe5, 0xc3, 0x85, 0xf3, 0x04, 0x59, 0xbd, 0x59, 0x56, 0xc0, 0xb5},
	{0x44, 0x71, 0xc1, 0x2b, 0xd4, 0x08, 0xf1, 0x25, 0xe5, 0x61, 0x89, 0x81, 0xcc},
	{0x78, 0x03, 0x91, 0x53, 0x67, 0xa5, 0x8a, 0xdf, 0xcc, 0x51, 0x51, 0xe0, 0xa4},
	{0x88, 0xef, 0x01, 0x1c, 0xbe, 0xe5, 0xd7, 0x14, 0x66, 0x04, 0x36, 0x46, 0x59},
	{0x8c, 0xd0, 0x1f, 0xe9, 0x5f, 0xc1, 0x2b, 0x81, 0x4c, 0xf1, 0xd2, 0xb7, 0x61},
	{0x23, 0x81, 0x33, 0xac, 0xf6, 0x91, 0x5b, 0x21, 0x25, 0x8a, 0x88, 0xce, 0x51},
	{0xf8, 0xe0, 0x5b, 0x77, 0x10, 0x01, 0x8c, 0x4c, 0xf0, 0xd7, 0x7e, 0x53, 0x04},
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
	};
