greatscottgadgets/ubertooth/host/ubertooth-tools/src/ubertooth-btle.c

/*
 * Copyright 2012-2016 Michael Ryan
 *
 * This file is part of Project Ubertooth.
 *
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
 * You should have received a copy of the GNU General Public License
 * along with this program; see the file COPYING.  If not, write to
 * the Free Software Foundation, Inc., 51 Franklin Street,
 * Boston, MA 02110-1301, USA.
 */

#include "ubertooth.h"
#include "ubertooth_callback.h"
#include <ctype.h>
#include <err.h>
#include <getopt.h>
#include <string.h>
#include <unistd.h>
#include <stdlib.h>
#include <signal.h>

int cancel_follow = 0;

// send SIGUSR1 to cancel following an active connection
static void cancel_follow_handler(int sig __attribute__((unused))) {
	cancel_follow = 1;
}

int running = 1;

static void quit(int sig __attribute__((unused))) {
	running = 0;
}

void print_mac(uint8_t *mac_address, int mask) {
	unsigned i;
	for (i = 0; i < 5; ++i)
		printf("%02x:", mac_address[i]);
	printf("%02x", mac_address[5]);
	if (mask >= 0)
		printf("/%u", mask);
}

int convert_mac_address(char *s, uint8_t *o, uint8_t *mask_out) {
	int i;
	char *mask_p;
	unsigned mask = 48; // default mask is entire BD ADDR

	if (strcmp(s, "none") == 0) {
		memset(o, 0, 6);
		mask_out = 0;
		return 1;
	}

	// if there is a mask included, parse it
	mask_p = strchr(s, '/');
	if (mask_p != NULL) {
		*mask_p = '\0';
		++mask_p;
		mask = strtoul(mask_p, NULL, 10);
		if (mask > 48) {
			printf("Error: MAC mask must be between 0 and 48\n");
			return 0;
		}
	}
	*mask_out = mask; // see above, default 48, otherwise user-supplied

	// validate length
	if (strlen(s) != 6 * 2 + 5) {
		printf("Error: MAC address is wrong length\n");
		return 0;
	}

	// validate hex chars and : separators
	for (i = 0; i < 6*3; i += 3) {
		if (!isxdigit(s[i]) ||
			!isxdigit(s[i+1])) {
			printf("Error: MAC address contains invalid character(s)\n");
			return 0;
		}
		if (i < 5*3 && s[i+2] != ':') {
			printf("Error: MAC address contains invalid character(s)\n");
			return 0;
		}
	}

	// sanity: checked; convert
	for (i = 0; i < 6; ++i) {
		unsigned byte;
		sscanf(&s[i*3], "%02x",&byte);
		o[i] = byte;
	}

	return 1;
}

static void usage(void)
{
	printf("ubertooth-btle - passive Bluetooth Low Energy monitoring\n");
	printf("Usage:\n");
	printf("\t-h this help\n");
	printf("\n");
	printf("    Major modes:\n");
	printf("\t-f follow connections\n");
	printf("\t-n don't follow, only print advertisements\n");
	printf("\t-p promiscuous: sniff active connections\n");
	printf("\n");
	printf("\t-a[address] get/set access address (example: -a8e89bed6)\n");
	printf("\t-s<address> faux slave mode, using MAC addr (example: -s22:44:66:88:aa:cc)\n");
	printf("\t-t<address> set connection following target (example: -t22:44:66:88:aa:cc/48)\n");
	printf("\t-tnone unset connection following target\n");
	printf("\n");
	printf("    Interference (use with -f or -p):\n");
	printf("\t-i interfere with one connection and return to idle\n");
	printf("\t-I interfere continuously\n");
	printf("\n");
	printf("    Data source:\n");
	printf("\t-U<0-7> set ubertooth device to use\n");
	printf("\n");
	printf("    Misc:\n");
	printf("\t-r<filename> capture packets to PCAPNG file\n");
	printf("\t-q<filename> capture packets to PCAP file (DLT_BLUETOOTH_LE_LL_WITH_PHDR)\n");
	printf("\t-c<filename> capture packets to PCAP file (DLT_PPI + DLT_BLUETOOTH_LE_LL)\n");
	printf("\t-A<index> advertising channel index (default 37)\n");
	printf("\t-v[01] verify CRC mode, get status or enable/disable\n");
	printf("\t-x<n> allow n access address offenses (default 32)\n");

	printf("\nIf an input file is not specified, an Ubertooth device is used for live capture.\n");
	printf("In get/set mode no capture occurs.\n");
}

int main(int argc, char *argv[])
{
	int opt;
	int do_follow, do_no_follow, do_promisc;
	int do_get_aa, do_set_aa;
	int do_crc;
	int do_adv_index;
	int do_slave_mode;
	int do_target;
	enum jam_modes jam_mode = JAM_NONE;
	int ubertooth_device = -1;
	ubertooth_t* ut = ubertooth_init();

	btle_options cb_opts = { .allowed_access_address_errors = 32 };

	int r;
	u32 access_address;
	uint8_t mac_address[6] = { 0, };
	uint8_t mac_mask = 0;

	do_follow = do_no_follow = do_promisc = 0;
	do_get_aa = do_set_aa = 0;
	do_crc = -1; // 0 and 1 mean set, 2 means get
	do_adv_index = 37;
	do_slave_mode = do_target = 0;

	while ((opt=getopt(argc,argv,"a::r:hfnpU:v::A:s:t:x:c:q:jJiI")) != EOF) {
		switch(opt) {
		case 'a':
			if (optarg == NULL) {
				do_get_aa = 1;
			} else {
				do_set_aa = 1;
				sscanf(optarg, "%08x", &access_address);
			}
			break;
		case 'f':
			do_follow = 1;
			break;
		case 'n':
			do_no_follow = 1;
			break;
		case 'p':
			do_promisc = 1;
			break;
		case 'U':
			ubertooth_device = atoi(optarg);
			break;
		case 'r':
			if (!ut->h_pcapng_le) {
				if (lell_pcapng_create_file(optarg, "Ubertooth", &ut->h_pcapng_le)) {
					err(1, "lell_pcapng_create_file: ");
				}
			}
			else {
				printf("Ignoring extra capture file: %s\n", optarg);
			}
			break;
		case 'q':
			if (!ut->h_pcap_le) {
				if (lell_pcap_create_file(optarg, &ut->h_pcap_le)) {
					err(1, "lell_pcap_create_file: ");
				}
			}
			else {
				printf("Ignoring extra capture file: %s\n", optarg);
			}
			break;
		case 'c':
			if (!ut->h_pcap_le) {
				if (lell_pcap_ppi_create_file(optarg, 0, &ut->h_pcap_le)) {
					err(1, "lell_pcap_ppi_create_file: ");
				}
			}
			else {
				printf("Ignoring extra capture file: %s\n", optarg);
			}
			break;
		case 'v':
			if (optarg)
				do_crc = atoi(optarg) ? 1 : 0;
			else
				do_crc = 2; // get
			break;
		case 'A':
			do_adv_index = atoi(optarg);
			if (do_adv_index < 37 || do_adv_index > 39) {
				printf("Error: advertising index must be 37, 38, or 39\n");
				usage();
				return 1;
			}
			break;
		case 's':
			do_slave_mode = 1;
			r = convert_mac_address(optarg, mac_address, &mac_mask);
			if (!r) {
				usage();
				return 1;
			}
			break;
		case 't':
			do_target = 1;
			r = convert_mac_address(optarg, mac_address, &mac_mask);
			if (!r) {
				usage();
				return 1;
			}
			break;
		case 'x':
			cb_opts.allowed_access_address_errors = (unsigned) atoi(optarg);
			if (cb_opts.allowed_access_address_errors > 32) {
				printf("Error: can tolerate 0-32 access address bit errors\n");
				usage();
				return 1;
			}
			break;
		case 'i':
		case 'j':
			jam_mode = JAM_ONCE;
			break;
		case 'I':
		case 'J':
			jam_mode = JAM_CONTINUOUS;
			break;
		case 'h':
		default:
			usage();
			return 1;
		}
	}


	r = ubertooth_connect(ut, ubertooth_device);
	if (r < 0) {
		usage();
		return 1;
	}

	r = ubertooth_check_api(ut);
	if (r < 0)
		return 1;

	// quit on ctrl-C
	signal(SIGINT, quit);
	signal(SIGQUIT, quit);
	signal(SIGTERM, quit);

	// cancel following on USR1
	signal(SIGUSR1, cancel_follow_handler);

	if (do_follow + do_no_follow + do_promisc > 1) {
		printf("Error: must choose one -f, -n, or -p, pick one pal\n");
		return 1;
	}

	// allow user to set target before following
	if (do_target) {
		r = cmd_btle_set_target(ut->devh, mac_address, mac_mask);
		if (r == 0) {
			if (mac_mask == 0) {
				printf("target cleared\n");
			} else {
				printf("target set to: ");
				print_mac(mac_address, mac_mask);
				printf("\n");
			}
		} else {
			printf("Unable to set target\n");
			return 1;
		}
	}

	if (do_follow || do_no_follow || do_promisc) {
		usb_pkt_rx rx;

		r = cmd_set_jam_mode(ut->devh, jam_mode);
		if (jam_mode != JAM_NONE && r != 0) {
			printf("Jamming not supported\n");
			return 1;
		}
		cmd_set_modulation(ut->devh, MOD_BT_LOW_ENERGY);

		if (do_follow || do_no_follow) {
			u16 channel;
			if (do_adv_index == 37)
				channel = 2402;
			else if (do_adv_index == 38)
				channel = 2426;
			else
				channel = 2480;
			cmd_set_channel(ut->devh, channel);
			cmd_btle_sniffing(ut->devh, do_follow);
		} else {
			cmd_btle_promisc(ut->devh);
		}

		// running can be changed by signal handler
		while (running) {
			if (cancel_follow) {
				cmd_cancel_follow(ut->devh);
				cancel_follow = 0;
			}
			int r = cmd_poll(ut->devh, &rx);
			if (r < 0) {
				printf("USB error\n");
				break;
			}
			if (r == sizeof(usb_pkt_rx)) {
				fifo_push(ut->fifo, &rx);
				cb_btle(ut, &cb_opts);
			}
			usleep(500);
		}
		ubertooth_stop(ut);
	}

	if (do_get_aa) {
		access_address = cmd_get_access_address(ut->devh);
		printf("Access address: %08x\n", access_address);
		return 0;
	}

	if (do_set_aa) {
		cmd_set_access_address(ut->devh, access_address);
		printf("access address set to: %08x\n", access_address);
	}

	if (do_crc >= 0) {
		int r;
		if (do_crc == 2) {
			r = cmd_get_crc_verify(ut->devh);
		} else {
			cmd_set_crc_verify(ut->devh, do_crc);
			r = do_crc;
		}
		printf("CRC: %sverify\n", r ? "" : "DO NOT ");
	}

	if (do_slave_mode) {
		u16 channel;
		if (do_adv_index == 37)
			channel = 2402;
		else if (do_adv_index == 38)
			channel = 2426;
		else
			channel = 2480;
		cmd_set_channel(ut->devh, channel);

		// flags: LE Limited Discovery
		uint8_t adv_data[] = { 0x02, 0x01, 0x05 };
		cmd_le_set_adv_data(ut->devh, adv_data, sizeof(adv_data));

		cmd_btle_slave(ut->devh, mac_address);
	}

	if (!(do_follow || do_no_follow || do_promisc || do_get_aa || do_set_aa ||
				do_crc >= 0 || do_slave_mode || do_target))
		usage();

	return 0;
}
