greatscottgadgets/ubertooth/host/ubertooth-tools/src/ubertooth-ego.c

/*
 * Copyright 2015 Mike Ryan
 *
 * This file is part of Project Ubertooth.
 *
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
 * You should have received a copy of the GNU General Public License
 * along with this program; see the file COPYING.  If not, write to
 * the Free Software Foundation, Inc., 51 Franklin Street,
 * Boston, MA 02110-1301, USA.
 */

#include "ubertooth.h"
#include "ubertooth_callback.h"
#include <ctype.h>
#include <err.h>
#include <getopt.h>
#include <string.h>
#include <unistd.h>
#include <stdlib.h>
#include <signal.h>

ubertooth_t* ut = NULL;
int running = 1;

void quit(int signo __attribute__((unused)))
{
	running = 0;
}

static void usage(void)
{
	printf("ubertooth-ego - Yuneec E-GO skateboard sniffing\n");
	printf("Usage:\n");
	printf("\t-h this help\n");
	printf("\n");
	printf("    Major modes:\n");
	printf("\t-f follow connections\n");
	printf("\t-r continuous rx on a single channel\n");
	printf("\t-i interfere\n");
	printf("\n");
	printf("    Options:\n");
	printf("\t-c <2402-2480> set channel in MHz (for continuous rx)\n");
	printf("\t-l <1-48> capture length (default: 18)\n");
	printf("\t-a <access_code> access code (default: 630f9ffe)\n");
}

int main(int argc, char *argv[])
{
	int opt;
	int do_mode = -1;
	int do_channel = 2418;
	int ubertooth_device = -1;
	uint8_t len = 18;
	char *access_code_str = NULL;
	uint8_t access_code[4];
	int access_code_len;
	int r;
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
